stefanoaz/Particle-counter-V1/ParticleCounter.kicad_sch

## KiCad design ParticleCounter.kicad_sch (2023-02-24)

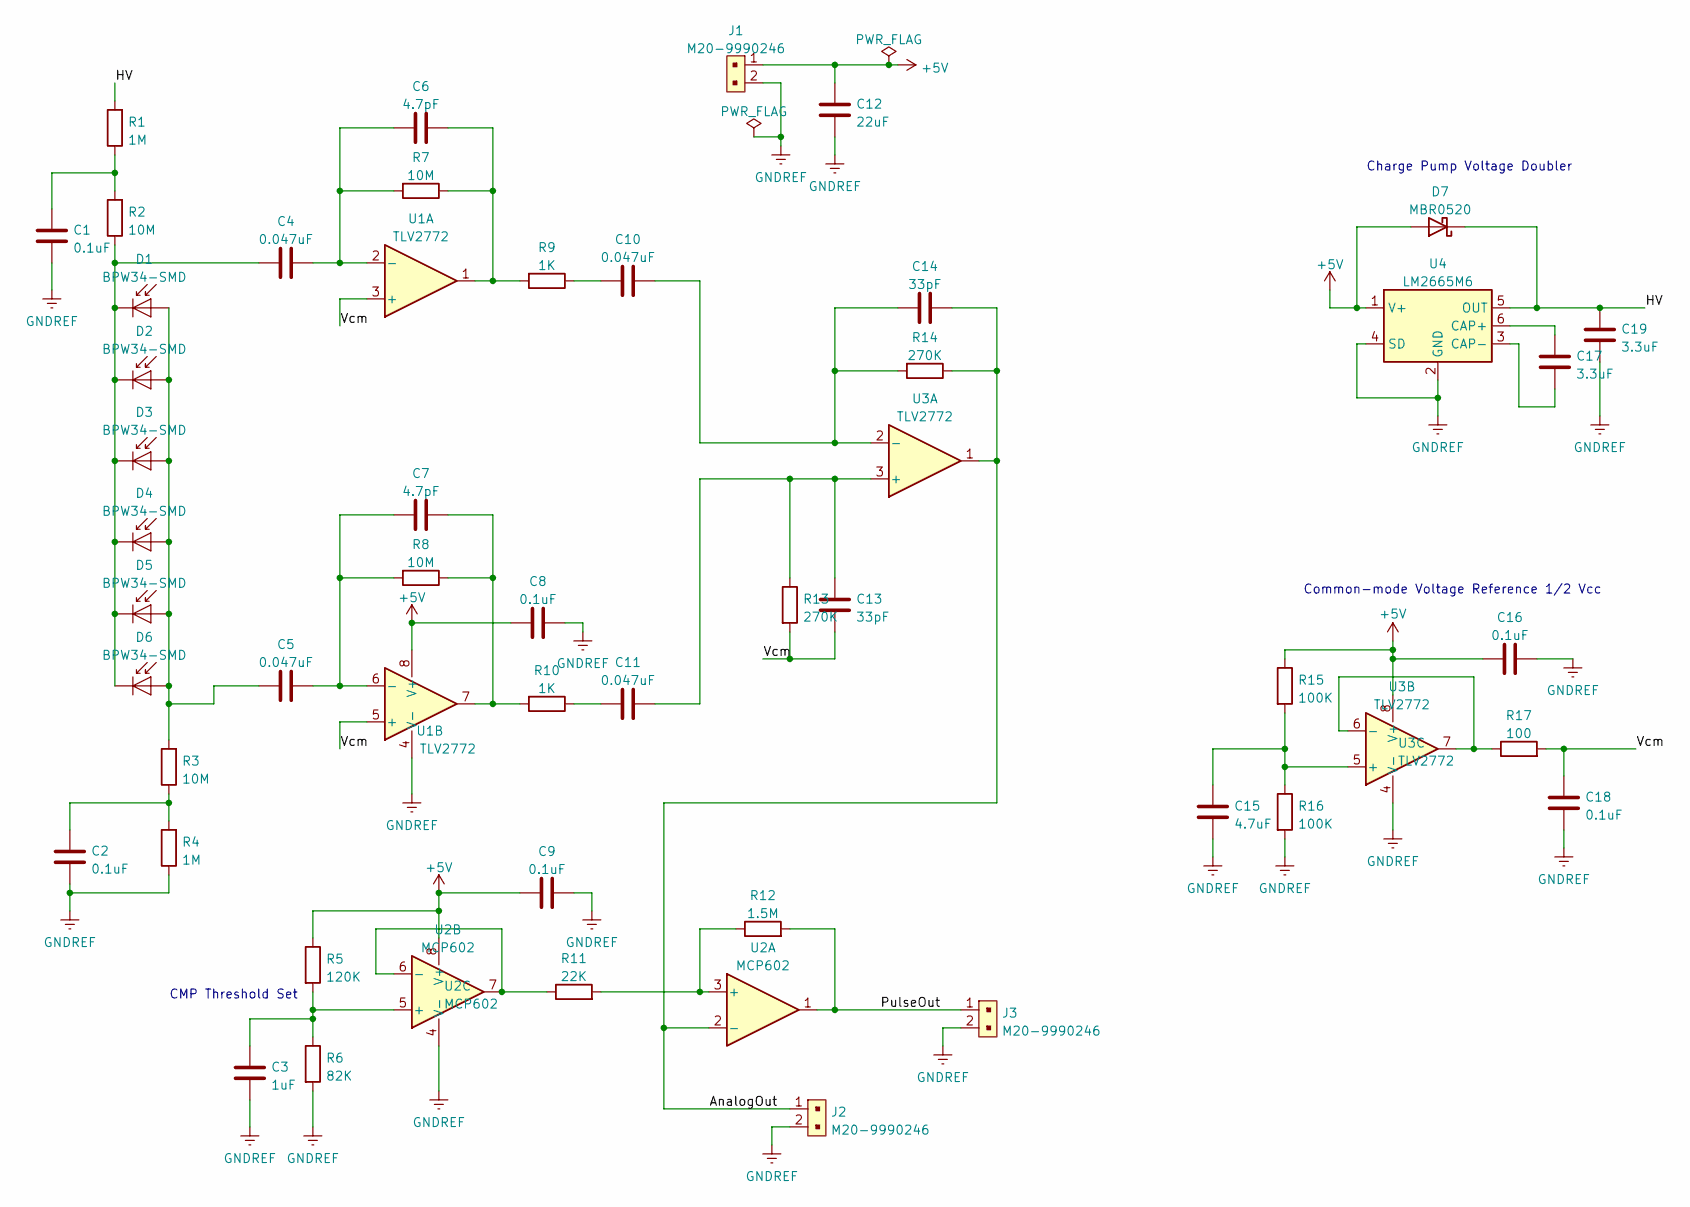
[picture p4: schematic ParticleCounter.kicad_sch]

Parts:
C1, C2, C18: 0.1uF; C_0805_2012Metric
C3: 1uF; C_0805_2012Metric
C4, C5, C10, C11: 0.047uF; C_0805_2012Metric
C6, C7: 4.7pF; C_0603_1608Metric
C8, C9, C16: 0.1uF; C_0603_1608Metric
C12: 22uF; C_0805_2012Metric
C13, C14: 33pF; C_0603_1608Metric
C15: 4.7uF; C_0805_2012Metric
C17, C19: 3.3uF; C_0805_2012Metric
D1, D2, D3, D4, D5, D6: BPW34-SMD; Osram_BPW34S-SMD
D7: MBR0520; D_SOD-123
J1, J2, J3: M20-9990246; PinHeader_1x2_P2.54mm; MPN M20-9990246; Digi-Key_PN 952-2262-ND
R1, R4: 1M; R_0603_1608Metric
R2, R3, R7, R8: 10M; R_0603_1608Metric
R5: 120K; R_0603_1608Metric
R6: 82K; R_0603_1608Metric
R9, R10: 1K; R_0603_1608Metric
R11: 22K; R_0603_1608Metric
R12: 1.5M; R_0603_1608Metric
R13, R14: 270K; R_0603_1608Metric
R15, R16: 100K; R_0603_1608Metric
R17: 100; R_0603_1608Metric
U1, U3: TLV2772; SO-8_3.9x4.9mm_P1.27mm
U2: MCP602; SO-8_3.9x4.9mm_P1.27mm
U4: LM2665M6; SOT-23-6

Connections:
+5V: C8.2, C9.2, C12.2, C16.1, D7.2 (A), J1.1, R5.1, R15.1, U1.8 (V+), U2.8 (V+), U3.8 (V+), U4.1 (V+)
AnalogOut: C14.1, J2.1, R14.1, U2.2 (-), U3.1
GNDREF: C1.2, C2.2, C3.2, C8.1, C9.1, C12.1, C15.1, C16.2, C18.1, C19.1, J1.2, J2.2, J3.2, R4.1, R6.2, R16.2, U1.4 (V-), U2.4 (V-), U3.4 (V-), U4.2 (GND), U4.4 (SD)
HV: C19.2, D7.1 (K), R1.2, U4.5 (OUT)
unnamed: C1.1, R1.1, R2.2
unnamed: C2.1, R3.1, R4.2
unnamed: C3.1, R5.2, R6.1, U2.5 (+)
unnamed: C4.1, D1.1 (K), D2.1 (K), D3.1 (K), D4.1 (K), D5.1 (K), D6.1 (K), R2.1
unnamed: C4.2, C6.2, R7.2, U1.2 (-)
unnamed: C5.1, D1.2 (A), D2.2 (A), D3.2 (A), D4.2 (A), D5.2 (A), D6.2 (A), R3.2
unnamed: C5.2, C7.2, R8.2, U1.6 (-)
unnamed: C6.1, R7.1, R9.2, U1.1
unnamed: C7.1, R8.1, R10.2, U1.7
unnamed: C10.1, R9.1
unnamed: C10.2, C14.2, R14.2, U3.2 (-)
unnamed: C11.1, R10.1
unnamed: C11.2, C13.2, R13.1, U3.3 (+)
unnamed: C15.2, R15.2, R16.1, U3.5 (+)
unnamed: C17.1, U4.3 (CAP-)
unnamed: C17.2, U4.6 (CAP+)
unnamed: R11.1, U2.6 (-), U2.7
unnamed: R11.2, R12.1, U2.3 (+)
unnamed: R17.1, U3.6 (-), U3.7
PulseOut: J3.1, R12.2, U2.1
Vcm: C13.1, C18.2, R13.2, R17.2, U1.3 (+), U1.5 (+)

Notes on the sheet:
Charge Pump Voltage Doubler
Common-mode Voltage Reference 1/2 Vcc
CMP Threshold Set
